gluonsandquarks/mirage/nudekoV3INK/.svg2shenzhen-cache/images/B.Mask_g23.png

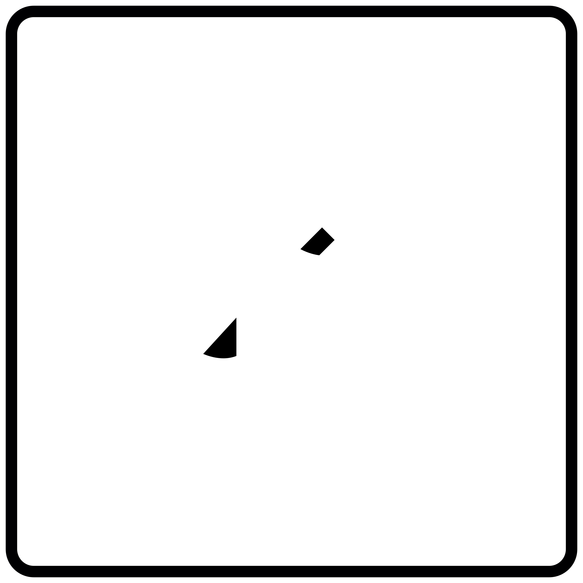
nudekoV3INK/.svg2shenzhen-cache/images/B.Mask_g23.png
