gluonsandquarks/mirage/refImages/3d.png

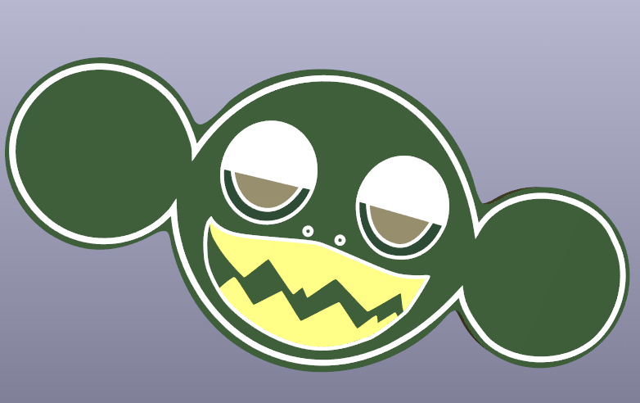
refImages/3d.png
