gluonsandquarks/mirage/refImages/pcb.png

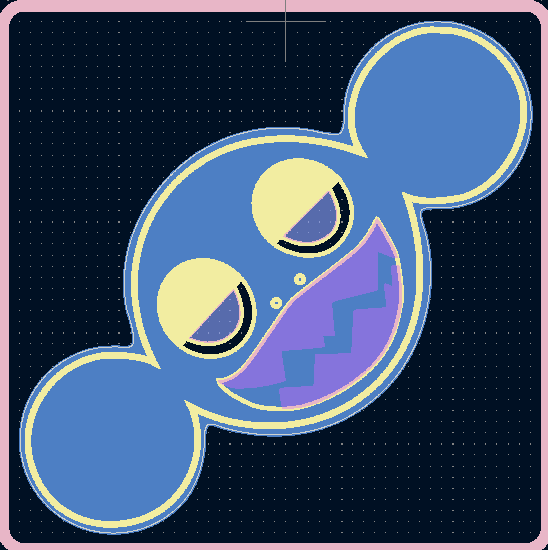
refImages/pcb.png
